ProjectBarks/subway-pcb/pcb/kicad projects files/controller.kicad_sch

## KiCad design pcb/kicad projects files/controller.kicad_sch (2026-03-16)

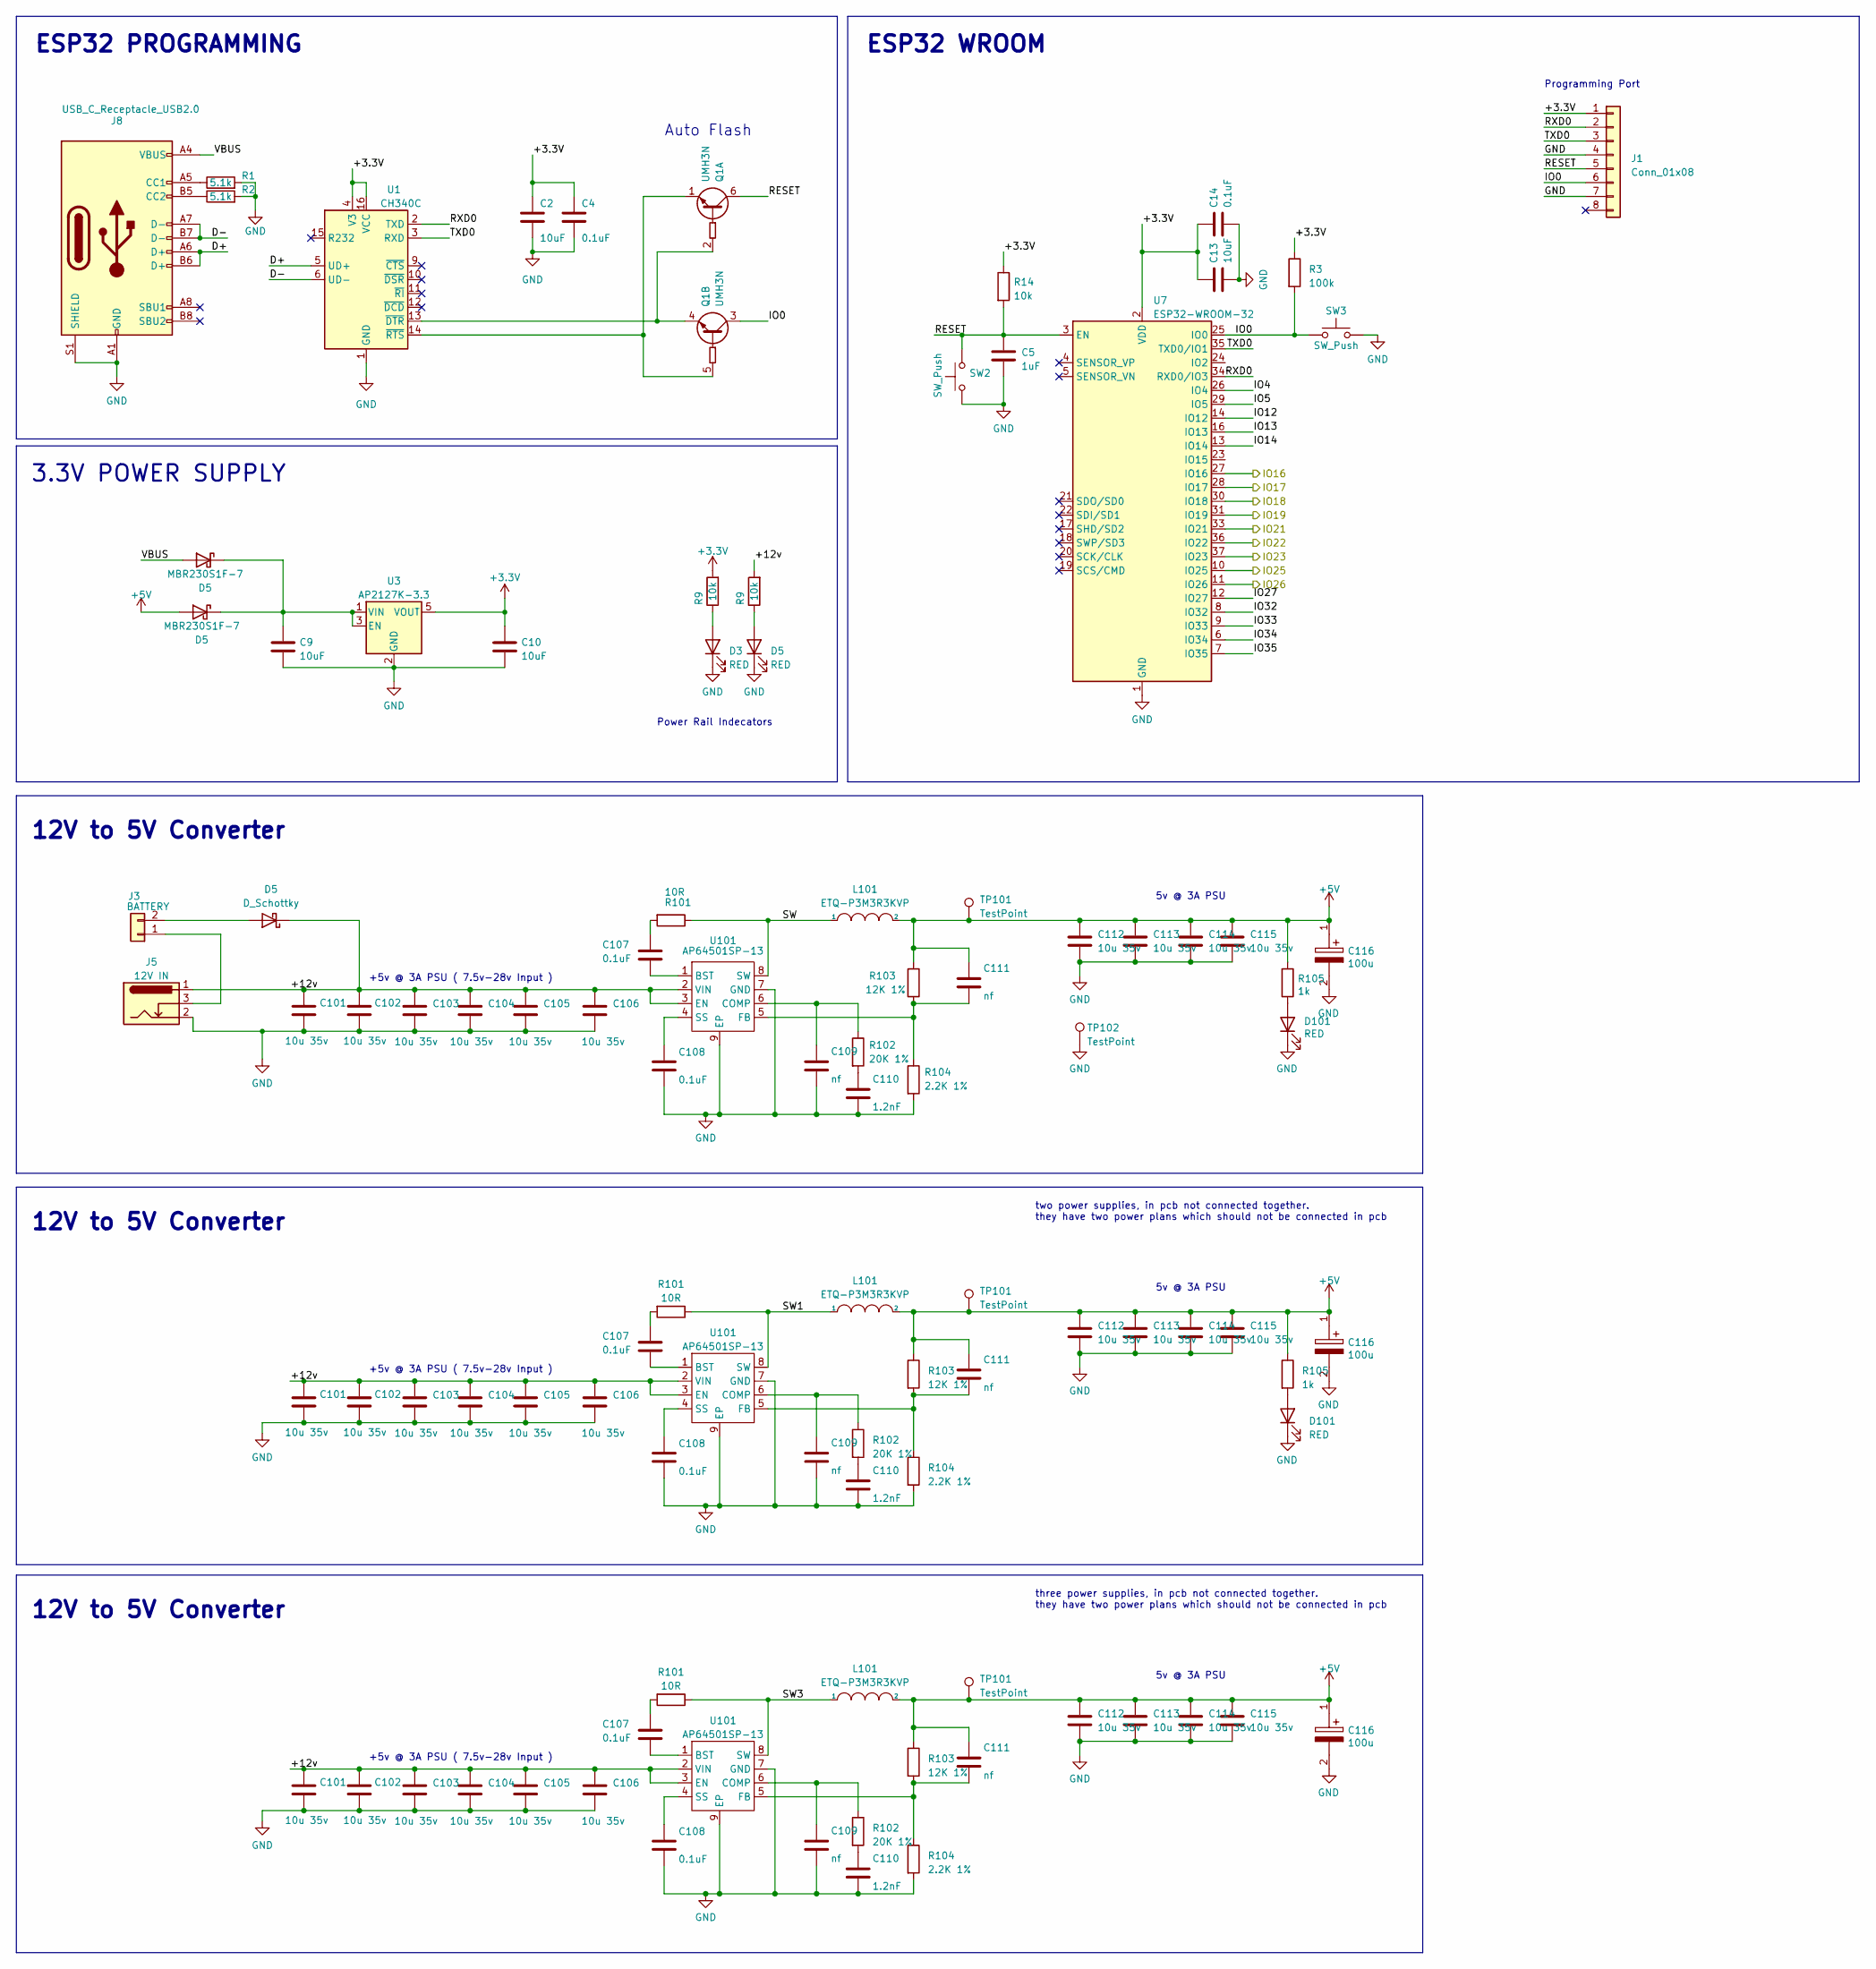
[picture p8: schematic controller.kicad_sch]

Parts:
C2, C9, C10, C13: 10uF; C_0603_1608Metric; MPN GRM188R61E106KA73D; LCSC C344022
C4, C14, C107, C108: 0.1uF; C_0402_1005Metric; MPN GRM155R71H104KE14D; LCSC C77020
C5: 1uF; C_0603_1608Metric; MPN CL10A105KB8NNNC; LCSC C15849
C101, C102, C103, C104, C105, C106, C112, C113, C114, C115: 10u 35v; C_0805_2012Metric; MPN GRM21BR6YA106ME43L; LCSC C361063
C109, C111: nf; C_0402_1005Metric; MPN dnp; LCSC dnp
C110: 1.2nF; C_0402_1005Metric; MPN 0402B122J500CT; LCSC C295919
C116: 100u; CP_EIA-3528-21_Kemet-B; MPN TPSB107K006R0250; LCSC C597710
D3, D101: RED; LED_0603_1608Metric; MPN XL-1608SURC-06; LCSC C965799
D5: MBR230S1F-7; D_SOD-123F; MPN MBR230S1F-7; LCSC C151335
J1: Conn_01x08; PinSocket_1x08_P2.54mm_Vertical; MPN dnp; LCSC DNP
J3: BATTERY; TerminalBlock_bornier-2_P5.08mm; MPN JL500-50802G01; LCSC C709041
J5: 12V IN; CONN-TH_DC-005-2.5A-2.0; MPN DC-005-2.5A-2.0; LCSC C319099
J8: USB_C_Receptacle_USB2.0; USB_C_Receptacle_G-Switch_GT-USB-7010ASV; MPN GT-USB-7010ASV; LCSC C2988369
L101: ETQ-P3M3R3KVP; ETQ-P3M_KVP; MPN ETQP3M3R3KVP; LCSC C542316
Q1: UMH3N; SOT-363_SC-70-6; MPN UMH3N; LCSC C62892
R1, R2: 5.1k; R_0402_1005Metric; MPN RC0402FR-075K1L; LCSC C105872
R3: 100k; R_0402_1005Metric; MPN RC0402FR-07100KL; LCSC C60491
R9, R14: 10k; R_0402_1005Metric; MPN RC0402FR-0710KL; LCSC C60490
R101: 10R; R_0402_1005Metric; MPN QR0402J10R0Q10Z; LCSC C176108
R102: 20K 1%; R_0402_1005Metric; MPN RC0402FR-0720KL; LCSC C93942
R103: 12K 1%; R_0402_1005Metric; MPN RC0402FR-0712KL; LCSC C114760
R104: 2.2K 1%; R_0402_1005Metric; MPN RC0402FR-072K2L; LCSC C114762
R105: 1k; R_0402_1005Metric; MPN CR0402FF1001G; LCSC C100195
SW2, SW3: SW_Push; SW_Push_1P1T_NO_CK_KMR2; MPN KMR221GLFS; LCSC C72443
TP101, TP102: TestPoint; TestPoint_Pad_2.0x2.0mm; MPN NA; LCSC NA
U1: CH340C; SOIC-16_3.9x9.9mm_P1.27mm; MPN CH340C; LCSC C7464026
U3: AP2127K-3.3; SOT-23-5; MPN AP2127K-3.3TRG1; LCSC C156285
U7: ESP32-WROOM-32; MPN ESP32-WROOM-32-N8; LCSC C529582
U101: AP64501SP-13; SOIC-8-1EP_3.9x4.9mm_P1.27mm_EP2.95x4.9mm_Mask2.71x3.4mm_Th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; MPN AP64501SP-13; LCSC C2071517

Connections:
+3.3V: C2.1, C4.1, C10.1, C13.1, C14.1, J1.1, R3.1, R9.2, R14.1, U1.4 (V3), U1.16 (VCC), U3.5 (VOUT), U7.2 (VDD)
+5V: C111.1, C112.1, C113.1, C114.1, C115.1, C116.1, D5.2 (A), L101.2, R103.1, R105.1, TP101.1
+12v: C101.1, C102.1, C103.1, C104.1, C105.1, C106.1, D5.1 (K), J5.1, R9.2, U101.2 (VIN), U101.3 (EN)
D+: J8.A6 (D+), J8.B6 (D+), U1.5 (UD+)
D-: J8.A7 (D-), J8.B7 (D-), U1.6 (UD-)
GND: C2.2, C4.2, C5.2, C9.2, C10.2, C13.2, C14.2, C101.2, C102.2, C103.2, C104.2, C105.2, C106.2, C108.2, C109.2, C110.2, C112.2, C113.2, C114.2, C115.2, C116.2, D3.1 (K), D5.1 (K), D101.1 (K), J1.4, J1.7, J5.2, J8.A1 (GND), J8.A12 (GND), J8.B1 (GND), J8.B12 (GND), J8.S1 (SHIELD), R1.2, R2.2, R104.2, SW2.1, SW3.2, TP102.1, U1.1 (GND), U3.2 (GND), U7.1 (GND), U7.15 (GND), U7.38 (GND), U7.39 (GND), U101.7 (GND), U101.9 (EP)
IO0: J1.6, Q1.3 (C2), R3.2, SW3.1, U7.25 (IO0)
IO4: U7.26 (IO4)
IO5: U7.29 (IO5)
IO12: U7.14 (IO12)
IO13: U7.16 (IO13)
IO14: U7.13 (IO14)
IO16: U7.27 (IO16)
IO17: U7.28 (IO17)
IO18: U7.30 (IO18)
IO19: U7.31 (IO19)
IO21: U7.33 (IO21)
IO22: U7.36 (IO22)
IO23: U7.37 (IO23)
IO25: U7.10 (IO25)
IO26: U7.11 (IO26)
IO27: U7.12 (IO27)
IO32: U7.8 (IO32)
IO33: U7.9 (IO33)
IO34: U7.6 (IO34)
IO35: U7.7 (IO35)
unnamed: C9.1, D5.1 (K), U3.1 (VIN), U3.3 (EN)
unnamed: C107.1, R101.2
unnamed: C107.2, U101.1 (BST)
unnamed: C108.1, U101.4 (SS)
unnamed: C109.1, R102.1, U101.6 (COMP)
unnamed: C110.1, R102.2
unnamed: C111.2, R103.2, R104.1, U101.5 (FB)
unnamed: D3.2 (A), R9.1
unnamed: D5.2 (A), J3.2, R9.1
unnamed: D101.2 (A), R105.2
unnamed: J3.1, J5.3
unnamed: J8.A5 (CC1), R1.1
unnamed: J8.B5 (CC2), R2.1
unnamed: Q1.1 (E1), Q1.5 (B2), U1.14 (~RTS)
unnamed: Q1.2 (B1), Q1.4 (E2), U1.13 (~DTR)
RESET: C5.1, J1.5, Q1.6 (C1), R14.2, SW2.2, U7.3 (EN)
RXD0: J1.2, U1.2 (TXD), U7.34 (RXD0/IO3)
SW: L101.1, R101.1, U101.8 (SW)
SW1: L101.1, R101.1, U101.8 (SW)
SW3: L101.1, R101.1, U101.8 (SW)
TXD0: J1.3, U1.3 (RXD), U7.35 (TXD0/IO1)
VBUS: D5.2 (A), J8.A4 (VBUS), J8.A9 (VBUS), J8.B4 (VBUS), J8.B9 (VBUS)

Notes on the sheet:
Programming Port
ESP32 PROGRAMMING
5v @ 3A PSU
three power supplies, in pcb not connected together. they have two power plans which should not be connected in pcb
Auto Flash
Power Rail Indecators
ESP32 WROOM
12V to 5V Converter
+5v @ 3A PSU ( 7.5v-28v Input )
two power supplies, in pcb not connected together. they have two power plans which should not be connected in pcb
3.3V POWER SUPPLY
