ProjectBarks/subway-pcb/pcb/kicad projects files/design.kicad_sch

## KiCad design pcb/kicad projects files/design.kicad_sch (2026-03-16)

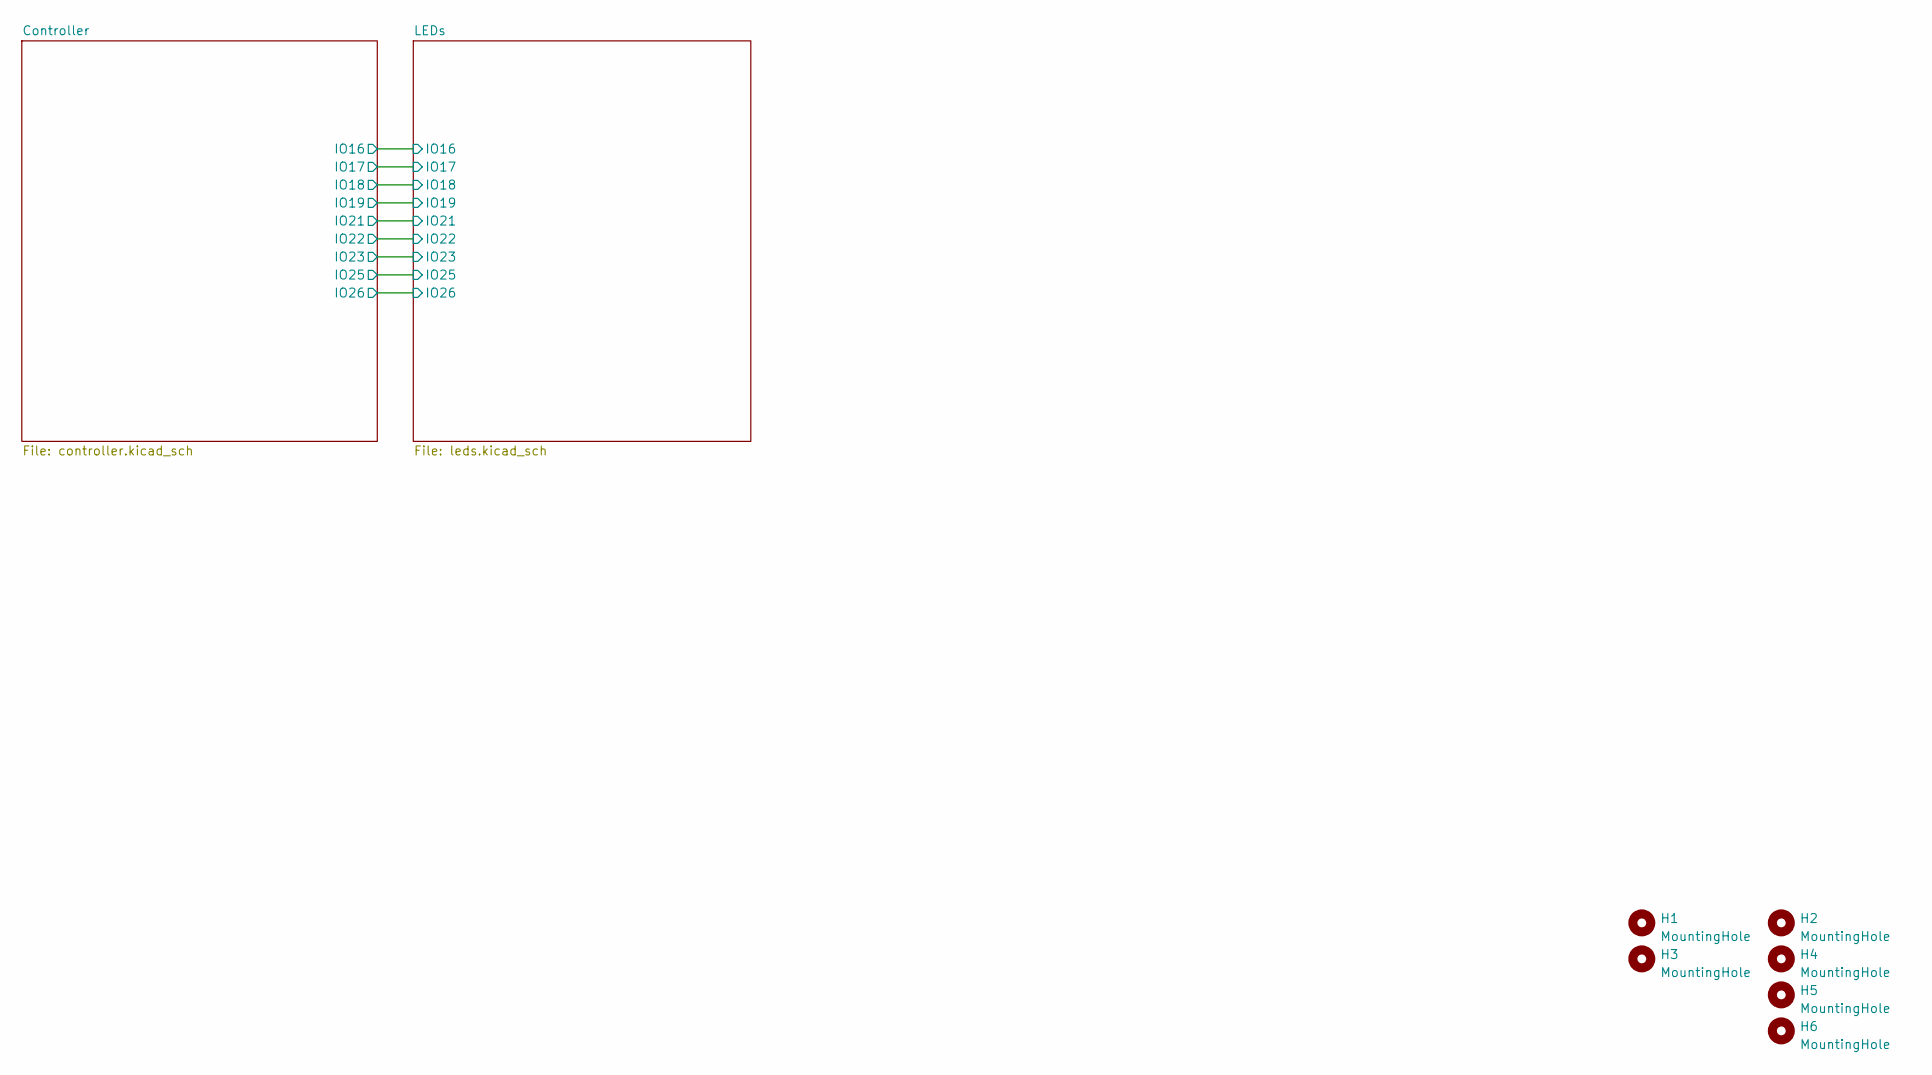
[picture p9: schematic design.kicad_sch]

Parts:
H1, H2, H3, H4, H5, H6: MountingHole; MountingHole_3.2mm_M3; MPN NA; LCSC NA
