ProjectBarks/subway-pcb/pcb/kicad projects files/esp32.kicad_sch

## KiCad design pcb/kicad projects files/esp32.kicad_sch (2026-03-16)

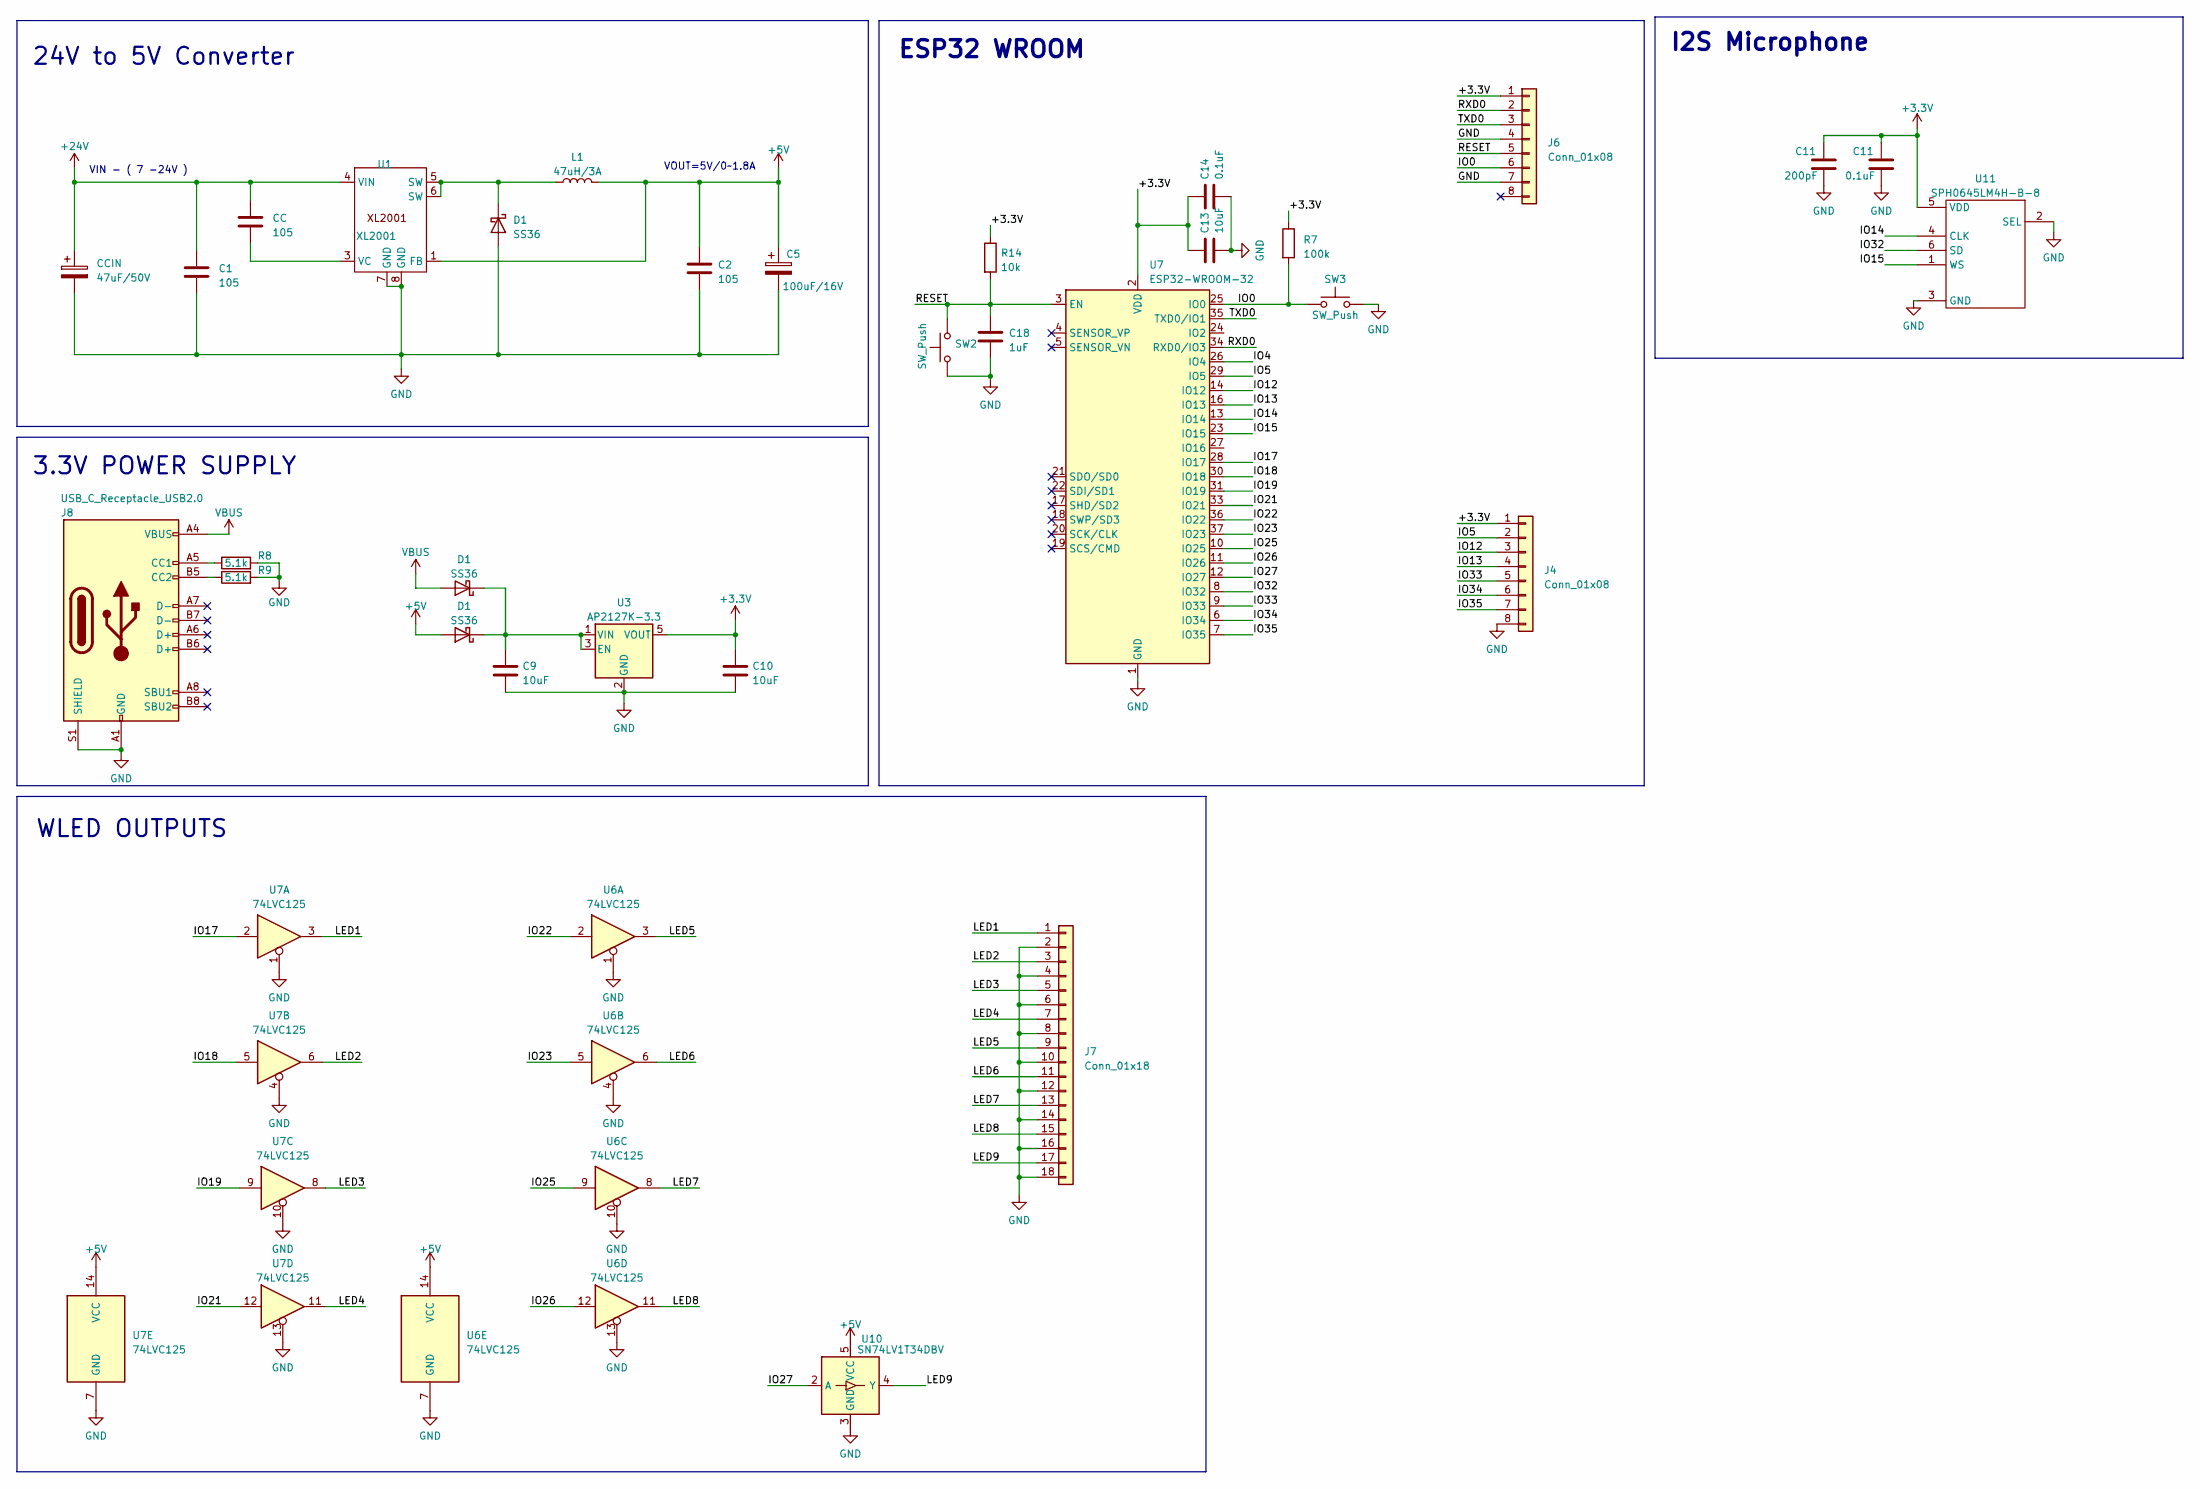
[picture p10: schematic esp32.kicad_sch]

Parts:
C1, C2: 105
C5: 100uF/16V
C9, C10, C13: 10uF; C_0603_1608Metric; MPN GRM188R61E106KA73D
C11: 200pF; C_0402_1005Metric; MPN GRT1555C1H201FA02D
C14: 0.1uF; C_0402_1005Metric; MPN GRM155R71H104KE14D
C18: 1uF; C_0603_1608Metric; MPN GRM188R61E105KA12D
CC: 105
CCIN: 47uF/50V
D1: SS36; D_SMA; MPN SS36; JLC Part C408260
J4: Conn_01x08; PinSocket_1x08_P2.54mm_Vertical; MPN dnp
J6: Conn_01x08; PinSocket_1x08_P2.54mm_Vertical
J7: Conn_01x18
J8: USB_C_Receptacle_USB2.0; TYPE-C-SMD_TYPE-C-6P; MPN TYPE-C 6P(073); JLC Part C668623
L1: 47uH/3A
R7: 100k; R_0603_1608Metric; MPN RC0603FR-07100KL
R8, R9: 5.1k; R_0402_1005Metric; MPN RC0402FR-075K1L
R14: 10k; R_0402_1005Metric; MPN RC0603FR-0710KL
SW2, SW3: SW_Push; SW_Push_1P1T_NO_CK_KMR2; MPN KMR221GLFS
U1: XL2001
U3: AP2127K-3.3; SOT-23-5; MPN AP2127K-3.3TRG1
U6, U7: 74LVC125; SOIC-14_3.9x8.7mm_P1.27mm; MPN SN74HCT125DR; JLC Part C352957
U10: SN74LV1T34DBV; SOT-23-5
U11: SPH0645LM4H-B-8; MPN SPH0645LM4H-B-8

Connections:
+3.3V: C10.1, C11.1, C13.1, C14.1, J4.1, J6.1, R7.1, R14.1, U3.5 (VOUT), U7.2, U11.5 (VDD)
+5V: C2.1, C5.1, D1.2 (A), L1.2, U1.1 (FB), U6.14 (VCC), U7.14 (VCC), U10.5 (VCC)
+24V: C1.1, CC.1, CCIN.1, U1.4 (VIN)
GND: C1.2, C2.2, C5.2, C9.2, C10.2, C11.2, C13.2, C14.2, C18.2, CCIN.2, D1.2 (A), J4.8, J6.4, J6.7, J7.2, J7.4, J7.6, J7.8, J7.10, J7.12, J7.14, J7.16, J7.18, J8.A1 (GND), J8.A12 (GND), J8.B1 (GND), J8.B12 (GND), J8.S1 (SHIELD), R8.2, R9.2, SW2.1, SW3.2, U1.7 (GND), U1.8 (GND), U3.2 (GND), U6.1, U6.4, U6.7 (GND), U6.10, U6.13, U7.1, U7.4, U7.7 (GND), U7.10, U7.13, U7.15 (GND), U7.38 (GND), U7.39 (GND), U10.3 (GND), U11.2 (SEL), U11.3 (GND)
IO0: J6.6, R7.2, SW3.1, U7.25 (IO0)
IO4: U7.26 (IO4)
IO5: J4.2, U7.29 (IO5)
IO12: J4.3, U7.14 (VCC)
IO13: J4.4, U7.16 (IO13)
IO14: U7.13, U11.4 (CLK)
IO15: U7.23 (IO15), U11.1 (WS)
IO17: U7.2, U7.28 (IO17)
IO18: U7.5, U7.30 (IO18)
IO19: U7.9, U7.31 (IO19)
IO21: U7.12, U7.33 (IO21)
IO22: U6.2, U7.36 (IO22)
IO23: U6.5, U7.37 (IO23)
IO25: U6.9, U7.10
IO26: U6.12, U7.11
IO27: U7.12, U10.2 (A)
IO32: U7.8, U11.6 (SD)
IO33: J4.5, U7.9
IO34: J4.6, U7.6
IO35: J4.7, U7.7 (GND)
LED1: J7.1, U7.3
LED2: J7.3, U7.6
LED3: J7.5, U7.8
LED4: J7.7, U7.11
LED5: J7.9, U6.3
LED6: J7.11, U6.6
LED7: J7.13, U6.8
LED8: J7.15, U6.11
LED9: J7.17, U10.4 (Y)
unnamed: C9.1, D1.1 (K), U3.1 (VIN), U3.3 (EN)
unnamed: CC.2, U1.3 (VC)
unnamed: D1.1 (K), L1.1, U1.5 (SW), U1.6 (SW)
unnamed: J8.A5 (CC1), R8.1
unnamed: J8.B5 (CC2), R9.1
RESET: C18.1, J6.5, R14.2, SW2.2, U7.3
RXD0: J6.2, U7.34 (RXD0/IO3)
TXD0: J6.3, U7.35 (TXD0/IO1)
VBUS: D1.2 (A), J8.A4 (VBUS), J8.A9 (VBUS), J8.B4 (VBUS), J8.B9 (VBUS)

Notes on the sheet:
24V to 5V Converter
ESP32 WROOM
VOUT=5V/0~1.8A
WLED OUTPUTS
VIN - ( 7 -24V )
3.3V POWER SUPPLY
I2S Microphone
