ProjectBarks/subway-pcb/pcb/kicad projects files/led.kicad_sch

## KiCad design pcb/kicad projects files/led.kicad_sch (2026-03-16)

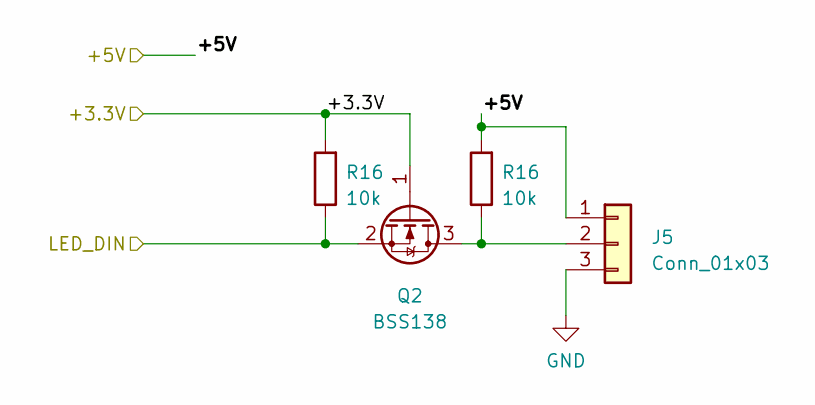
[picture p11: schematic led.kicad_sch]

Parts:
J5: Conn_01x03; JST_PH_S3B-PH-K_1x03_P2.00mm_Horizontal; MPN S3B-PH-K-S
Q2: BSS138; SOT-23; MPN BSS138
R16: 10k; R_0402_1005Metric; MPN RC0603FR-0710KL

Connections:
+3.3V: Q2.1 (G), R16.2
+5V: J5.1, R16.2
GND: J5.3
LED_DIN: Q2.2 (S), R16.1
unnamed: J5.2, Q2.3 (D), R16.1
