ProjectBarks/subway-pcb/pcb/kicad projects files/motor.kicad_sch

## KiCad design pcb/kicad projects files/motor.kicad_sch (2026-03-16)

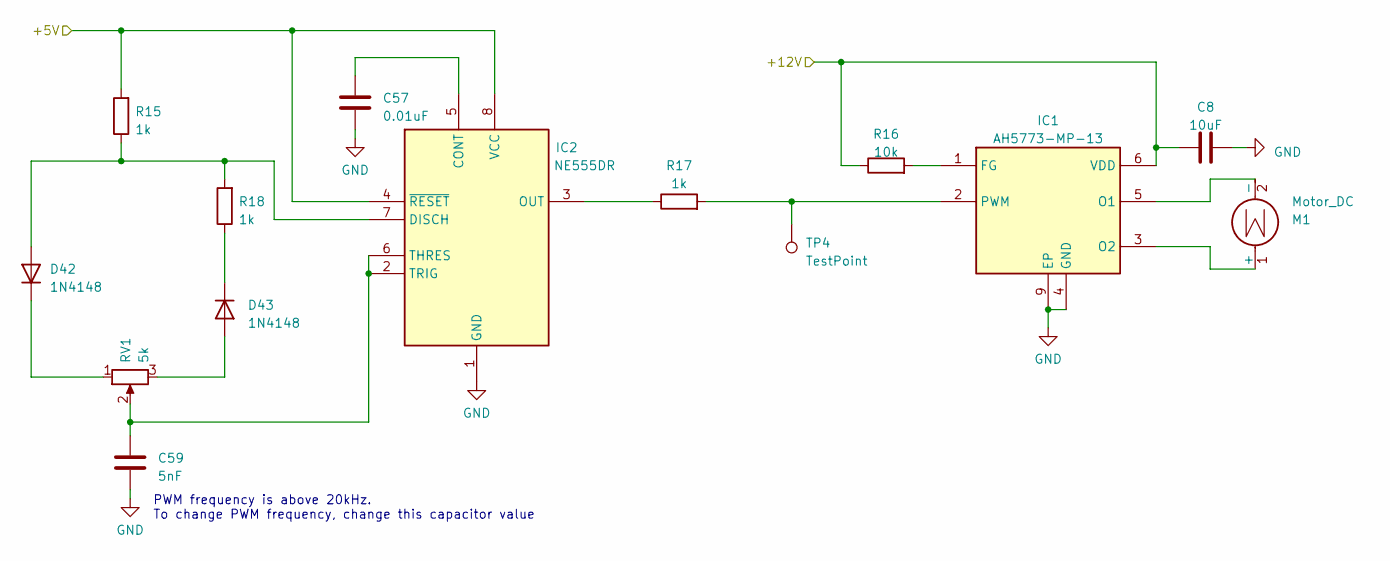
[picture p12: schematic motor.kicad_sch]

Parts:
C8: 10uF; C_1206_3216Metric; MPN GRM31CR71C106KAC7L
C57: 0.01uF; C_0603_1608Metric; MPN GRM188R71H103KA01D
C59: 5nF; C_0805_2012Metric_Pad1.18x1.45mm_HandSolder; MPN 0805B502K500NT
D42, D43: 1N4148; D_SOD-123; MPN 1N4148W-HE3-08
IC1: AH5773-MP-13; SOP65P490X110-9N; Mouser Part Number 621-AH5773-MP-13
IC2: NE555DR; SOIC127P600X175-8N; Mouser Part Number 595-NE555DR
M1: Motor_DC; JST_PH_S2B-PH-K_1x02_P2.00mm_Horizontal; MPN S2B-PH-K-S
R15, R17, R18: 1k; R_0402_1005Metric; MPN RC0402FR-071KL
R16: 10k; R_0402_1005Metric; MPN RC0603FR-0710KL
RV1: 5k; PTV09A4020FB103; MPN PTV09A-4220F-B502
TP4: TestPoint; TestPoint_Pad_1.5x1.5mm; MPN dnp

Connections:
+5V: IC2.4 (~RESET), IC2.8 (VCC), R15.2
+12V: C8.1, IC1.6 (VDD), R16.1
GND: C8.2, C57.2, C59.2, IC1.4 (GND), IC1.9 (EP), IC2.1 (GND)
unnamed: C57.1, IC2.5 (CONT)
unnamed: C59.1, IC2.2 (TRIG), IC2.6 (THRES), RV1.2
unnamed: D42.1 (K), RV1.1
unnamed: D42.2 (A), IC2.7 (DISCH), R15.1, R18.2
unnamed: D43.1 (K), R18.1
unnamed: D43.2 (A), RV1.3
unnamed: IC1.1 (FG), R16.2
unnamed: IC1.2 (PWM), R17.2, TP4.1
unnamed: IC1.3 (O2), M1.1 (+)
unnamed: IC1.5 (O1), M1.2 (-)
unnamed: IC2.3 (OUT), R17.1

Notes on the sheet:
PWM frequency is above 20kHz. To change PWM frequency, change this capacitor value
