ProjectBarks/subway-pcb/pcb/kicad projects files/power.kicad_sch

## KiCad design pcb/kicad projects files/power.kicad_sch (2026-03-16)

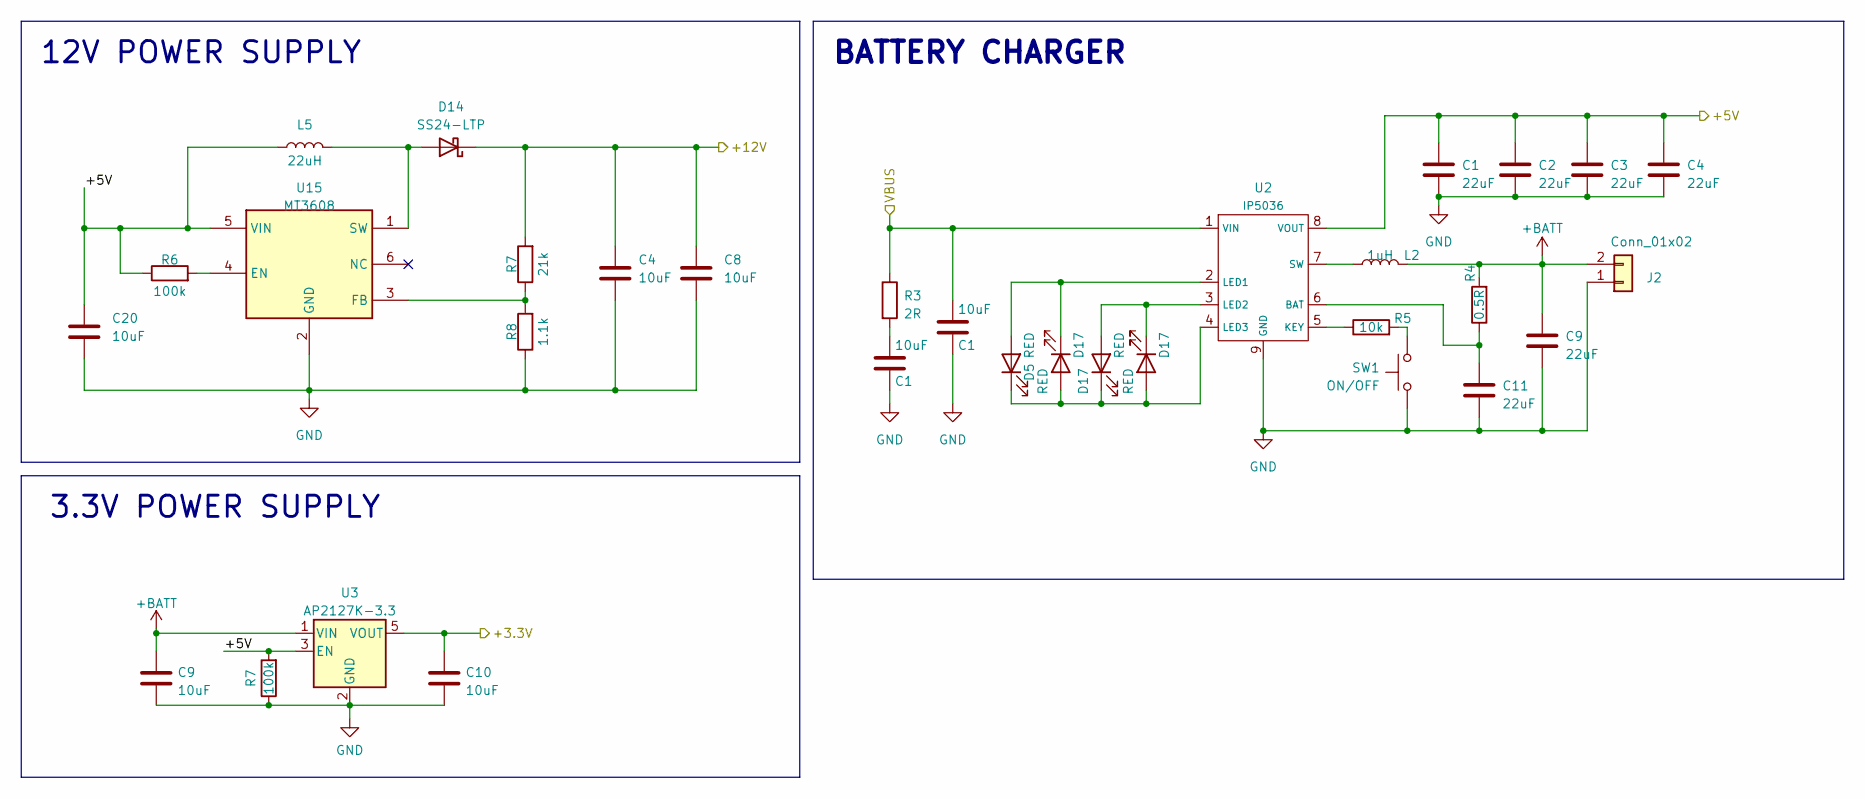
[picture p13: schematic power.kicad_sch]

Parts:
C1, C2, C3, C4, C11: 22uF; C_1206_3216Metric; MPN CL31A226MOCLNNC
C8, C20: 10uF; C_1206_3216Metric; MPN GRM31CR71C106KAC7L
C9, C10: 10uF; C_0603_1608Metric; MPN GRM188R61E106KA73D
D5, D17: RED; 155124RS73200A; MPN 155124RS73200A
D14: SS24-LTP; D_SMA; MPN SS34-E3/9AT
J2: Conn_01x02; JST_PH_S2B-PH-K_1x02_P2.00mm_Horizontal; MPN S2B-PH-K-S
L2: 1uH; L_1008_2520Metric; MPN SPH252010H1R0MT
L5: 22uH; ASPI6045T220MT; Mouser Part Number 815-ASP6045T-220M-T
R3: 2R; R_0603_1608Metric; MPN AC0603JR-072RL
R4: 0.5R; R_0603_1608Metric; MPN RL0603JR-070R5L
R5: 10k; R_0402_1005Metric; MPN RC0603FR-0710KL
R6: 100k; R_0402_1005Metric; MPN RC0603FR-07100KL
R7: 21k; R_0402_1005Metric; MPN RC0402FR-0721KL
R8: 1.1k; R_0402_1005Metric; MPN RC0402FR-071K1L
SW1: ON/OFF; JST_PH_S2B-PH-K_1x02_P2.00mm_Horizontal; MPN S2B-PH-K-S
U2: IP5036; ESOP-8_L4.9-W3.9-P1.27-LS6.0-BL-EP; MPN IP5036
U3: AP2127K-3.3; SOT-23-5; MPN AP2127K-3.3TRG1
U15: MT3608; SOT-23-6; MPN MT3608

Connections:
+3.3V: C10.1, U3.5 (VOUT)
+5V: C1.1, C2.1, C3.1, C4.1, C20.1, L5.1, R6.1, R7.2, U2.8 (VOUT), U3.3 (EN), U15.5 (VIN)
+12V: C4.1, C8.1, D14.1 (K), R7.2
+BATT: C9.1, J2.2, L2.2, R4.2, U3.1 (VIN)
GND: C1.2, C2.2, C3.2, C4.2, C8.2, C9.2, C10.2, C11.2, C20.2, J2.1, R7.1, R8.1, SW1.2, U2.9 (GND), U3.2 (GND), U15.2 (GND)
unnamed: C1.1, R3.2
unnamed: C11.1, R4.1, U2.6 (BAT)
unnamed: D14.2 (A), L5.2, U15.1 (SW)
unnamed: D5.1 (K), D5.2 (A), D17.1 (K), D17.2 (A), U2.2 (LED1), U2.3 (LED2), U2.4 (LED3)
unnamed: L2.1, U2.7 (SW)
unnamed: R5.1, U2.5 (KEY)
unnamed: R5.2, SW1.1
unnamed: R6.2, U15.4 (EN)
unnamed: R7.1, R8.2, U15.3 (FB)
VBUS: C1.1, R3.1, U2.1 (VIN)

Notes on the sheet:
12V POWER SUPPLY
3.3V POWER SUPPLY
BATTERY CHARGER
